myhumankit/Canne_a_son/PCB/LibComponent/3Dmodel/TC1014-1.8VCT713.STEP

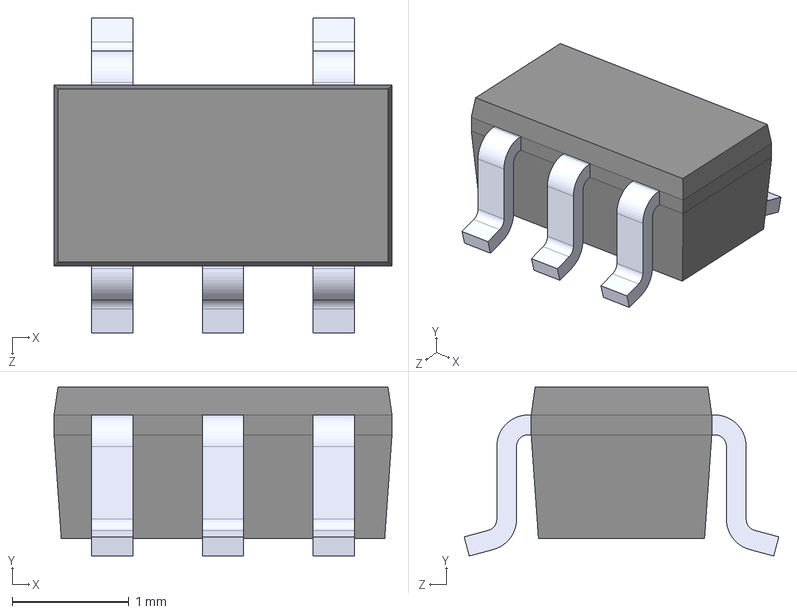
[picture p15: CAD file, 2022-09-29]
PCB/LibComponent/3Dmodel/TC1014-1.8VCT713.STEP
2.90 x 1.45 x 2.70 mm
