myhumankit/Canne_a_son/PCB/LibComponent/3Dmodel/PCA9306D_112.STEP

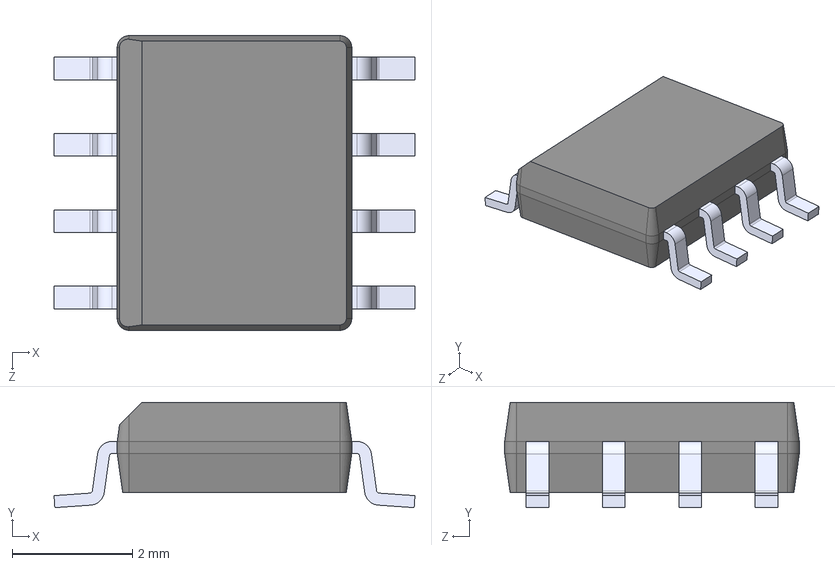
[picture p16: CAD file, 2022-09-29]
PCB/LibComponent/3Dmodel/PCA9306D_112.STEP
6.00 x 1.75 x 4.90 mm
