myhumankit/Canne_a_son/PCB/LibComponent/3Dmodel/5034800800.STEP

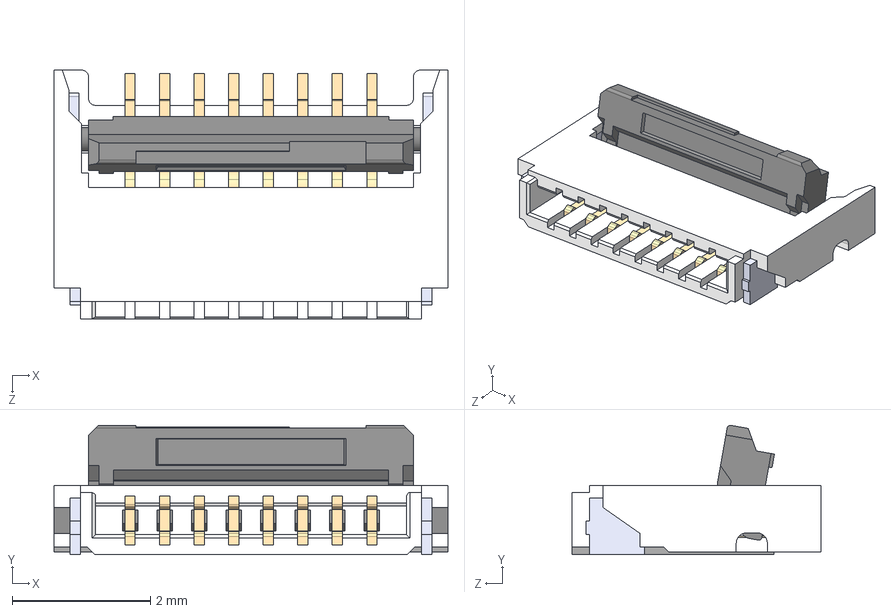
[picture p17: CAD file, 2022-09-29]
PCB/LibComponent/3Dmodel/5034800800.STEP
5.70 x 1.87 x 3.60 mm
